dabigatran/modular-amplituner/speakers/BROMO.pdf

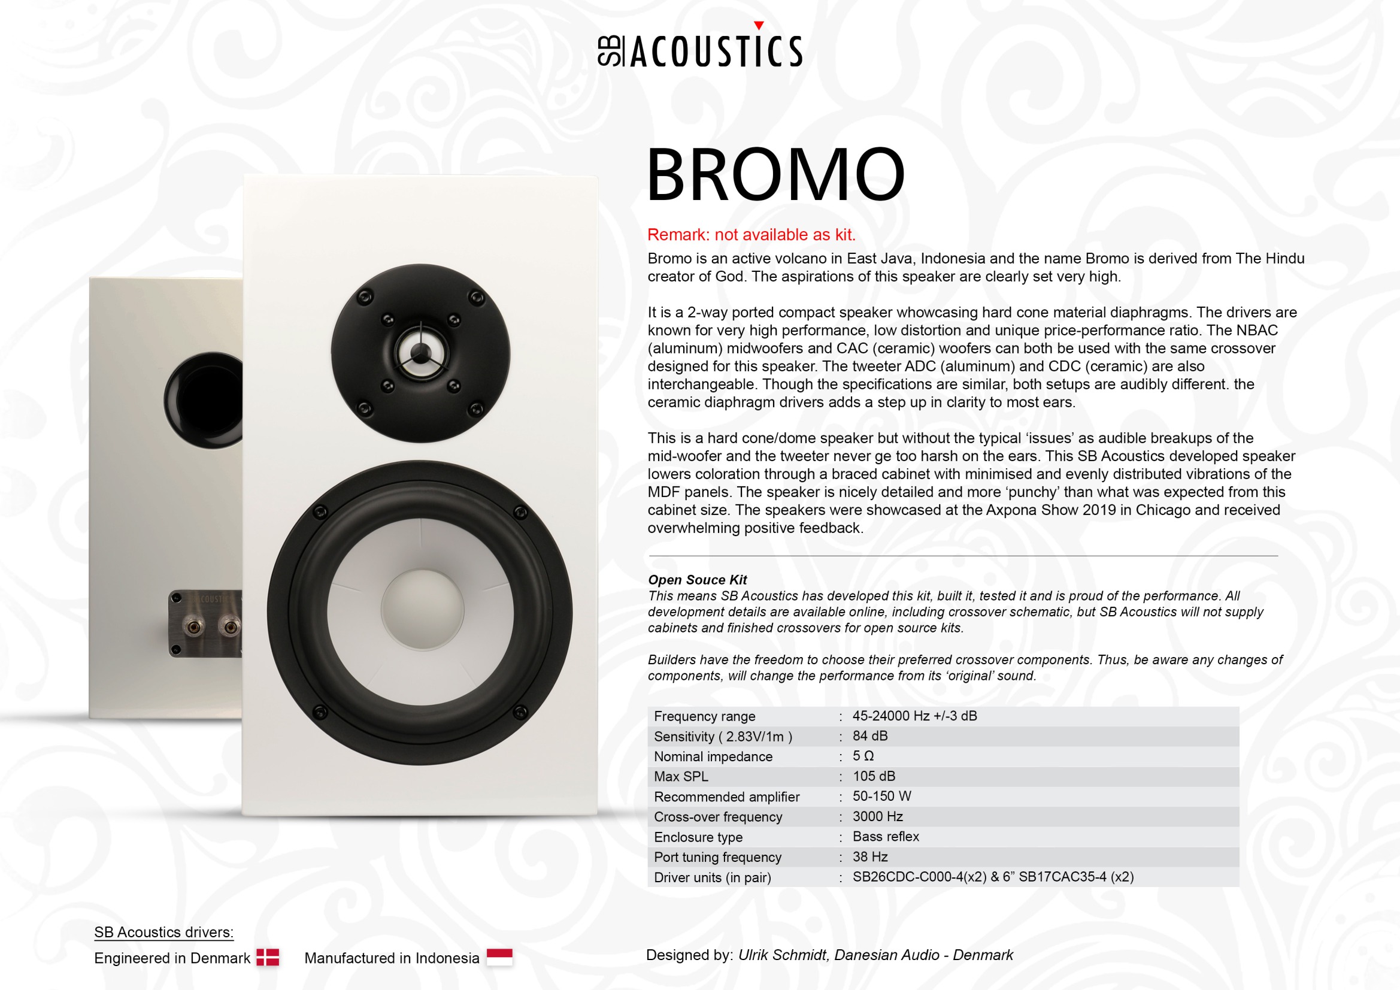
[picture p68: page 1]
