dabigatran/modular-amplituner/speakers/Bromo-Cabinet-Drawing.pdf

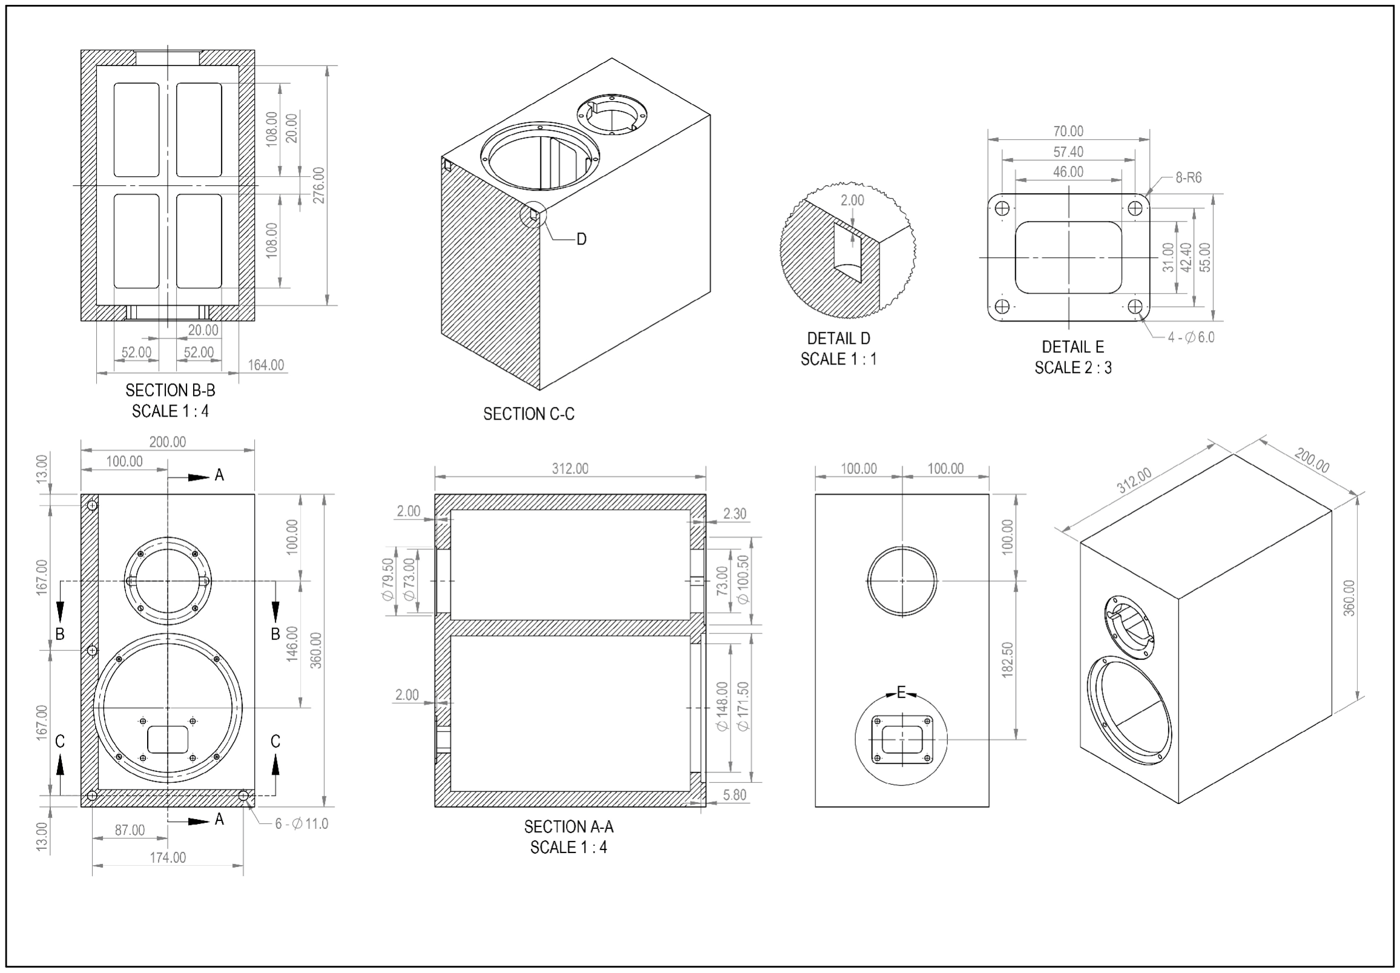
[picture p94: page 1]
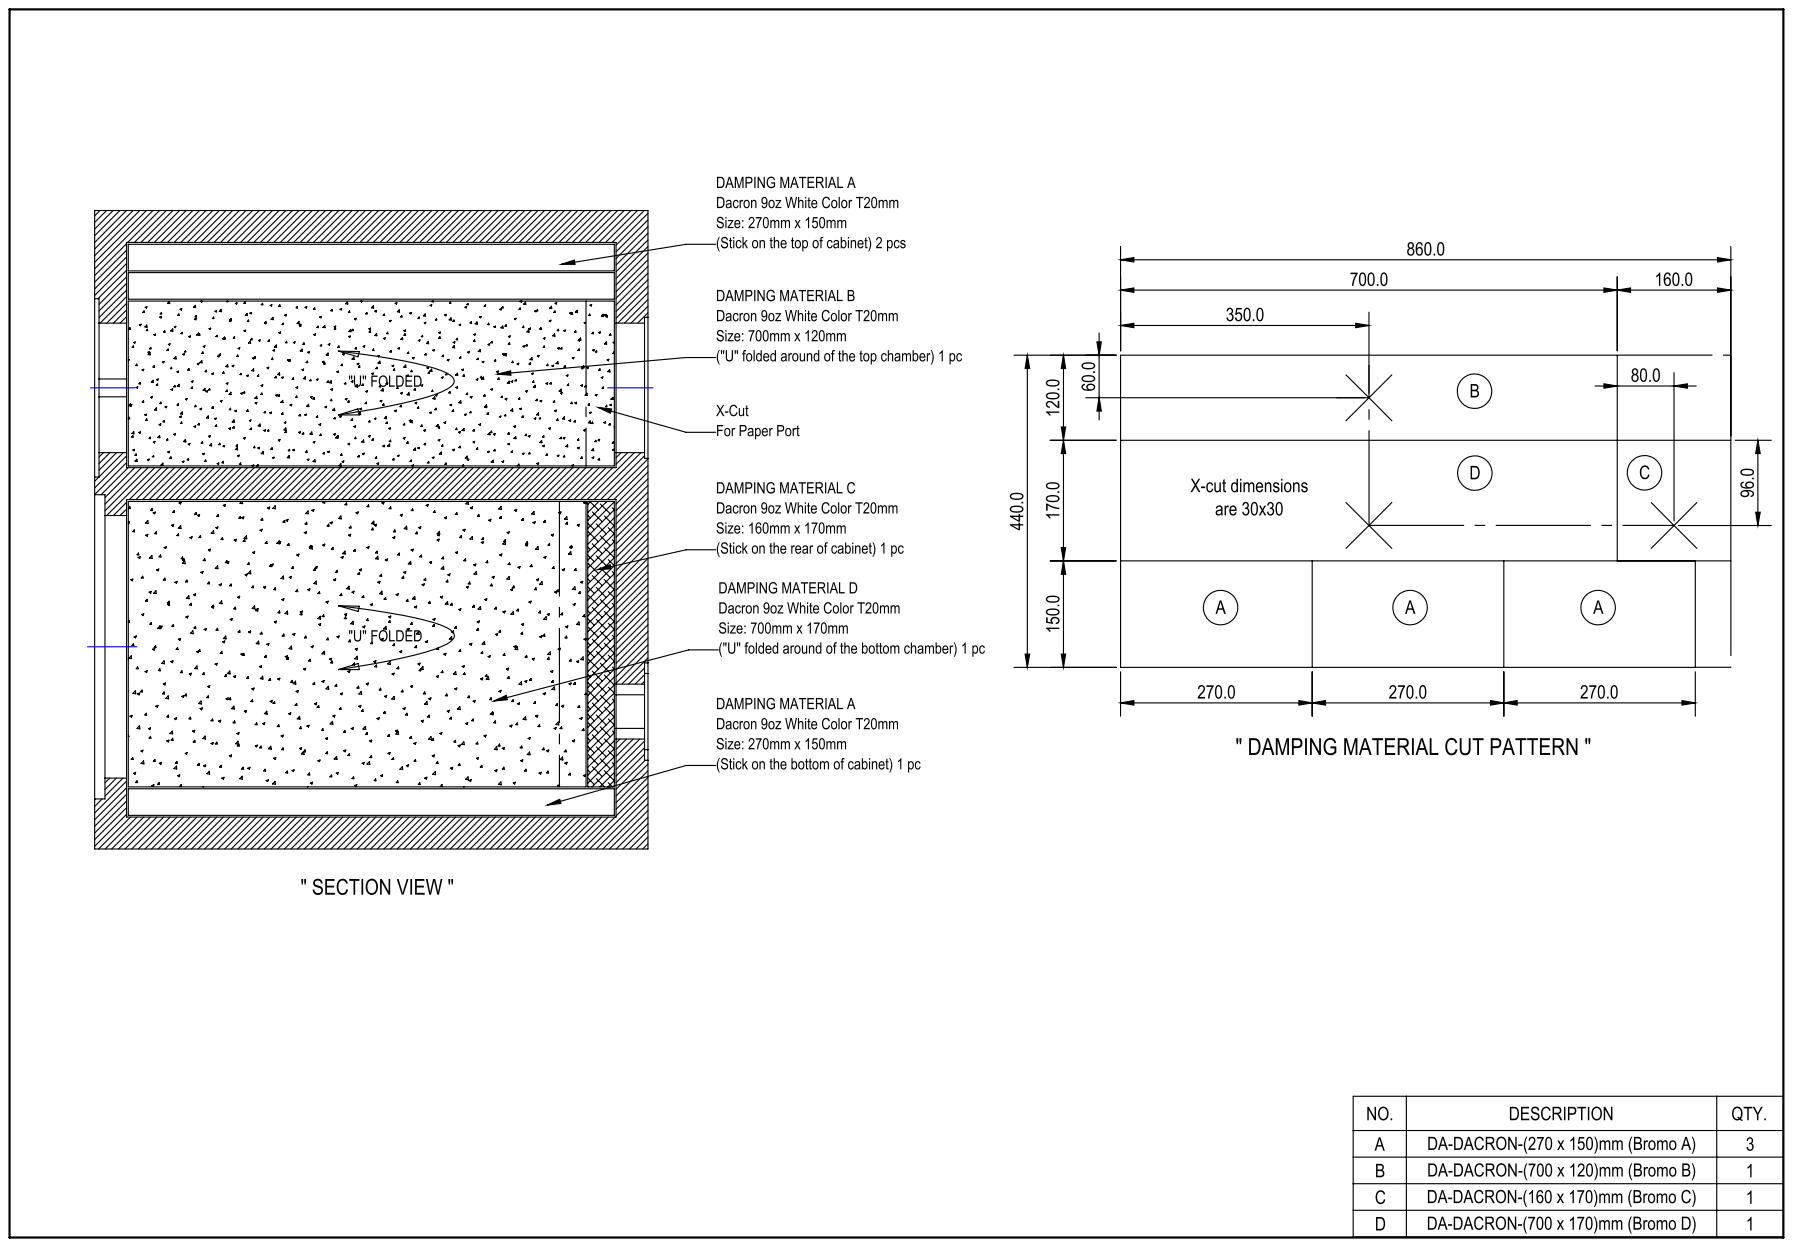
[picture p95: page 2]
